ejangelico/SSRTeensy/widaq-magis-ssr-v2b/system_diagram.png

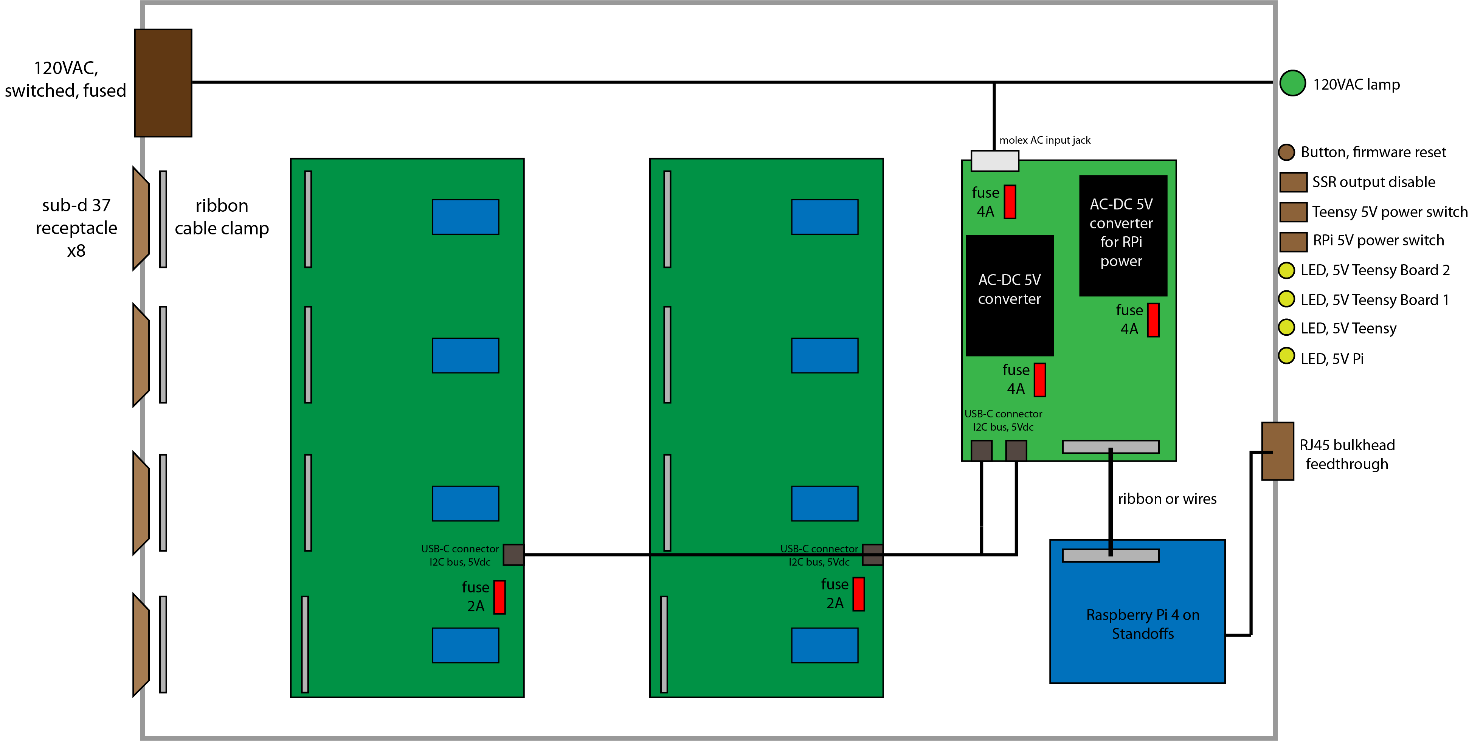
widaq-magis-ssr-v2b/system_diagram.png
