ejangelico/SSRTeensy/widaq-magis-ssr-v2b/assembly_diagrams/Screenshot 2023-06-01 at 9.44.38 AM.png

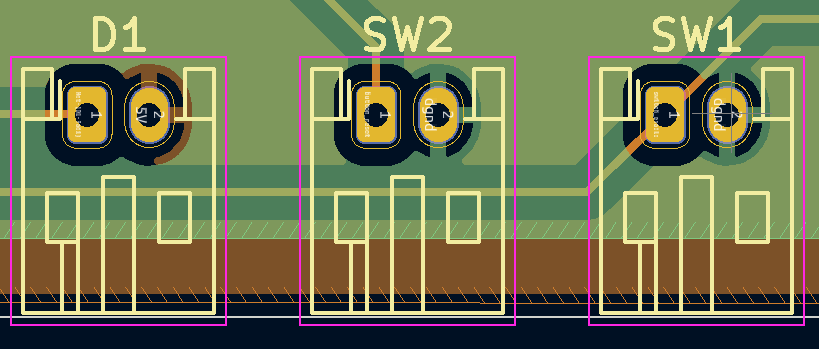
widaq-magis-ssr-v2b/assembly_diagrams/Screenshot 2023-06-01 at 9.44.38 AM.png
