ejangelico/SSRTeensy/widaq-magis-ssr-v2b/v2a-power-board/box-assembly/Screenshot 2023-04-19 at 4.38.34 PM.png

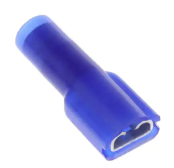
widaq-magis-ssr-v2b/v2a-power-board/box-assembly/Screenshot 2023-04-19 at 4.38.34 PM.png
