ejangelico/SSRTeensy/widaq-magis-ssr-v2b/output_files/2-21-22/widaq-magis-ssr-v1b-F_SilkS.pdf

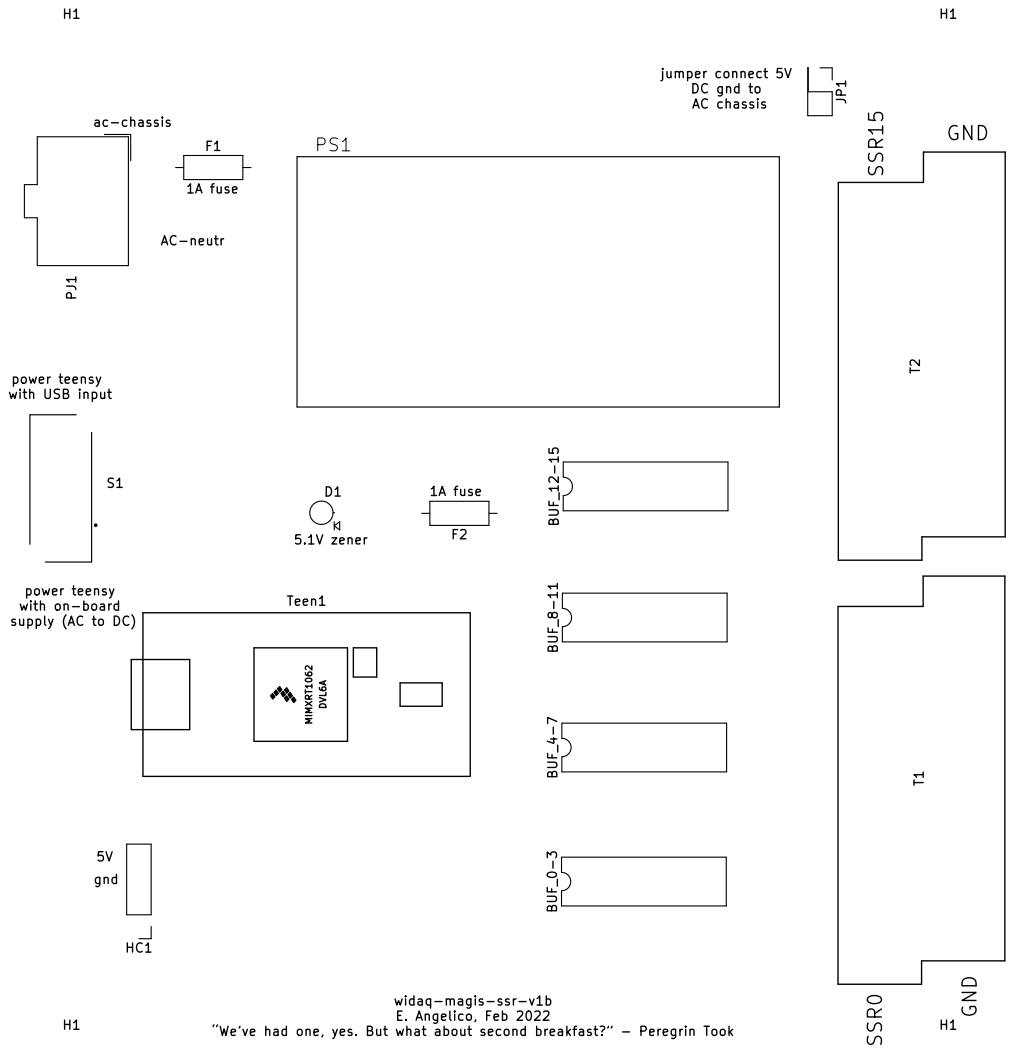
[picture p46: page 1]

jumper connect 5V DC gnd to AC chassis gnd

widaq-magis-ssr-v1b E. Angelico, Feb 2022 Weve had one, yes. But what about second breakfast? - Peregrin Took
