ejangelico/SSRTeensy/widaq-magis-ssr-v2b/output_files/drafting/widaq-magis-ssr-v1a.pdf

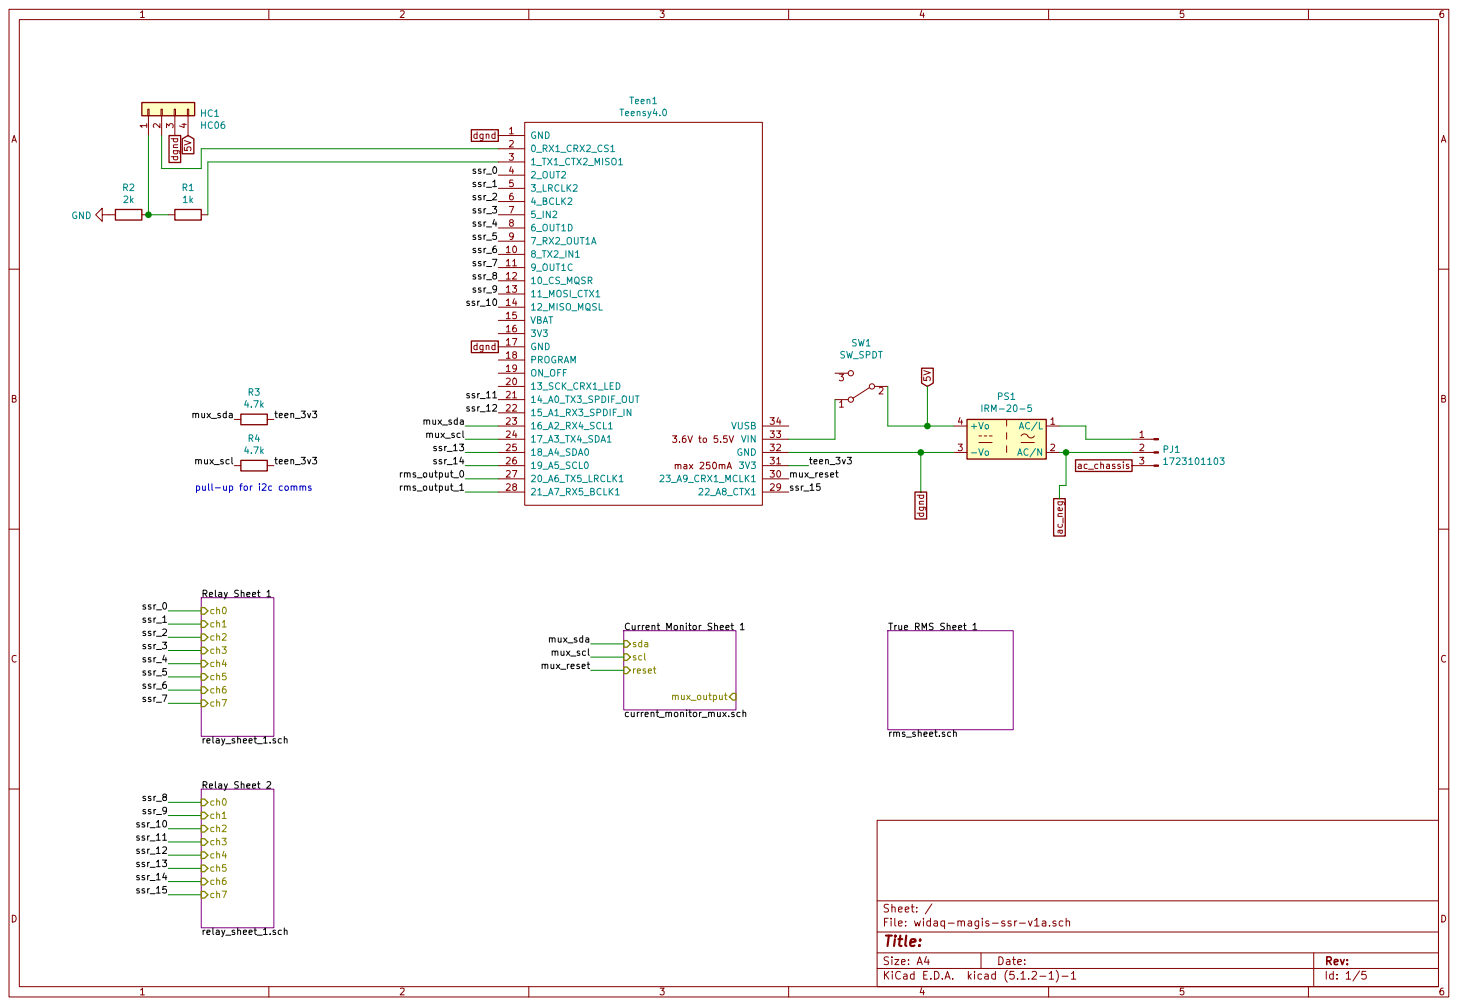
[picture p47: page 1]

pull-up for i2c comms

File: widaq-magis-ssr-v1a.sch Sheet: /

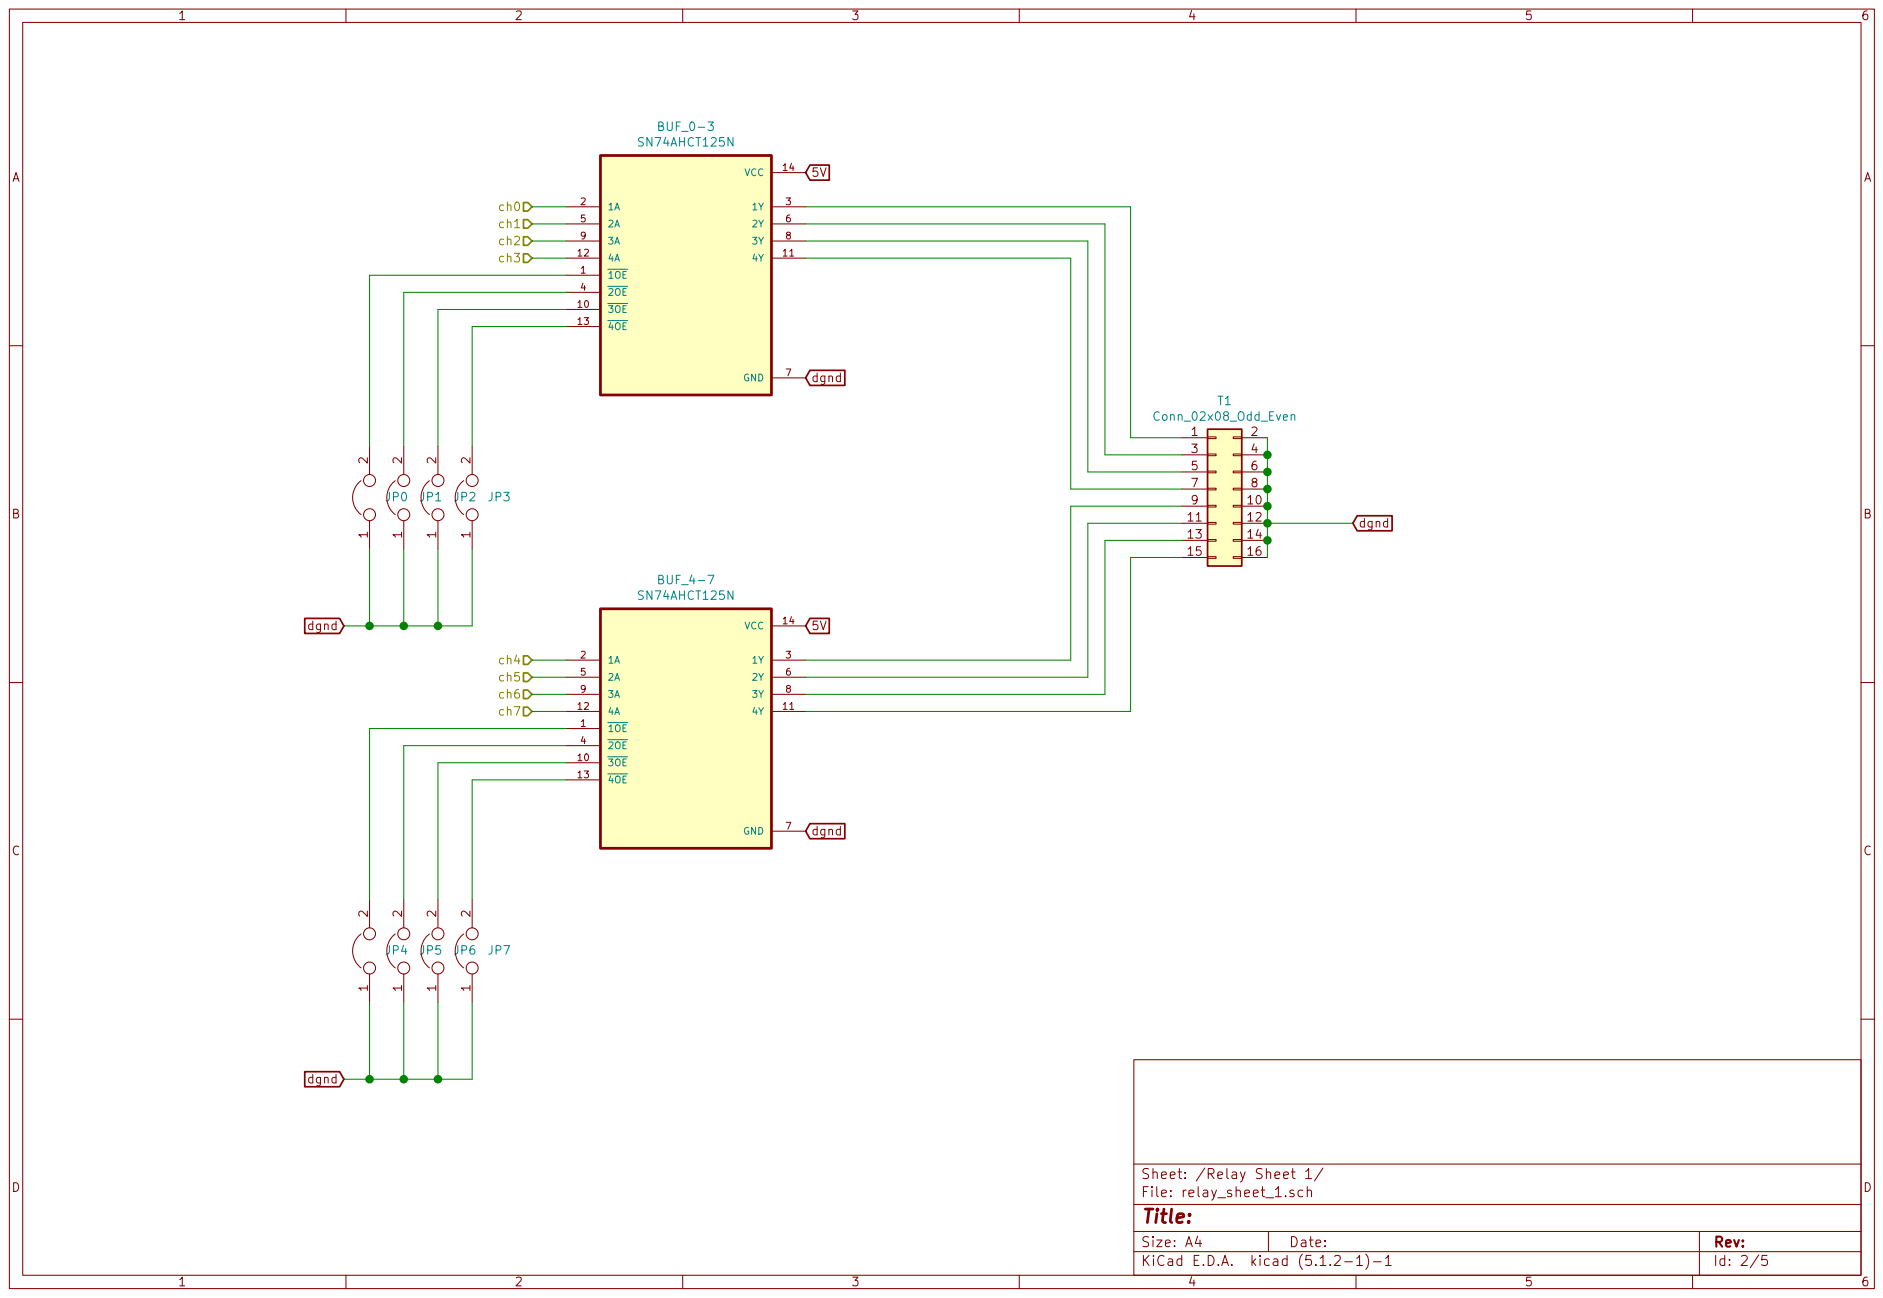
[picture p48: page 2]

11 | 12
13 | 14

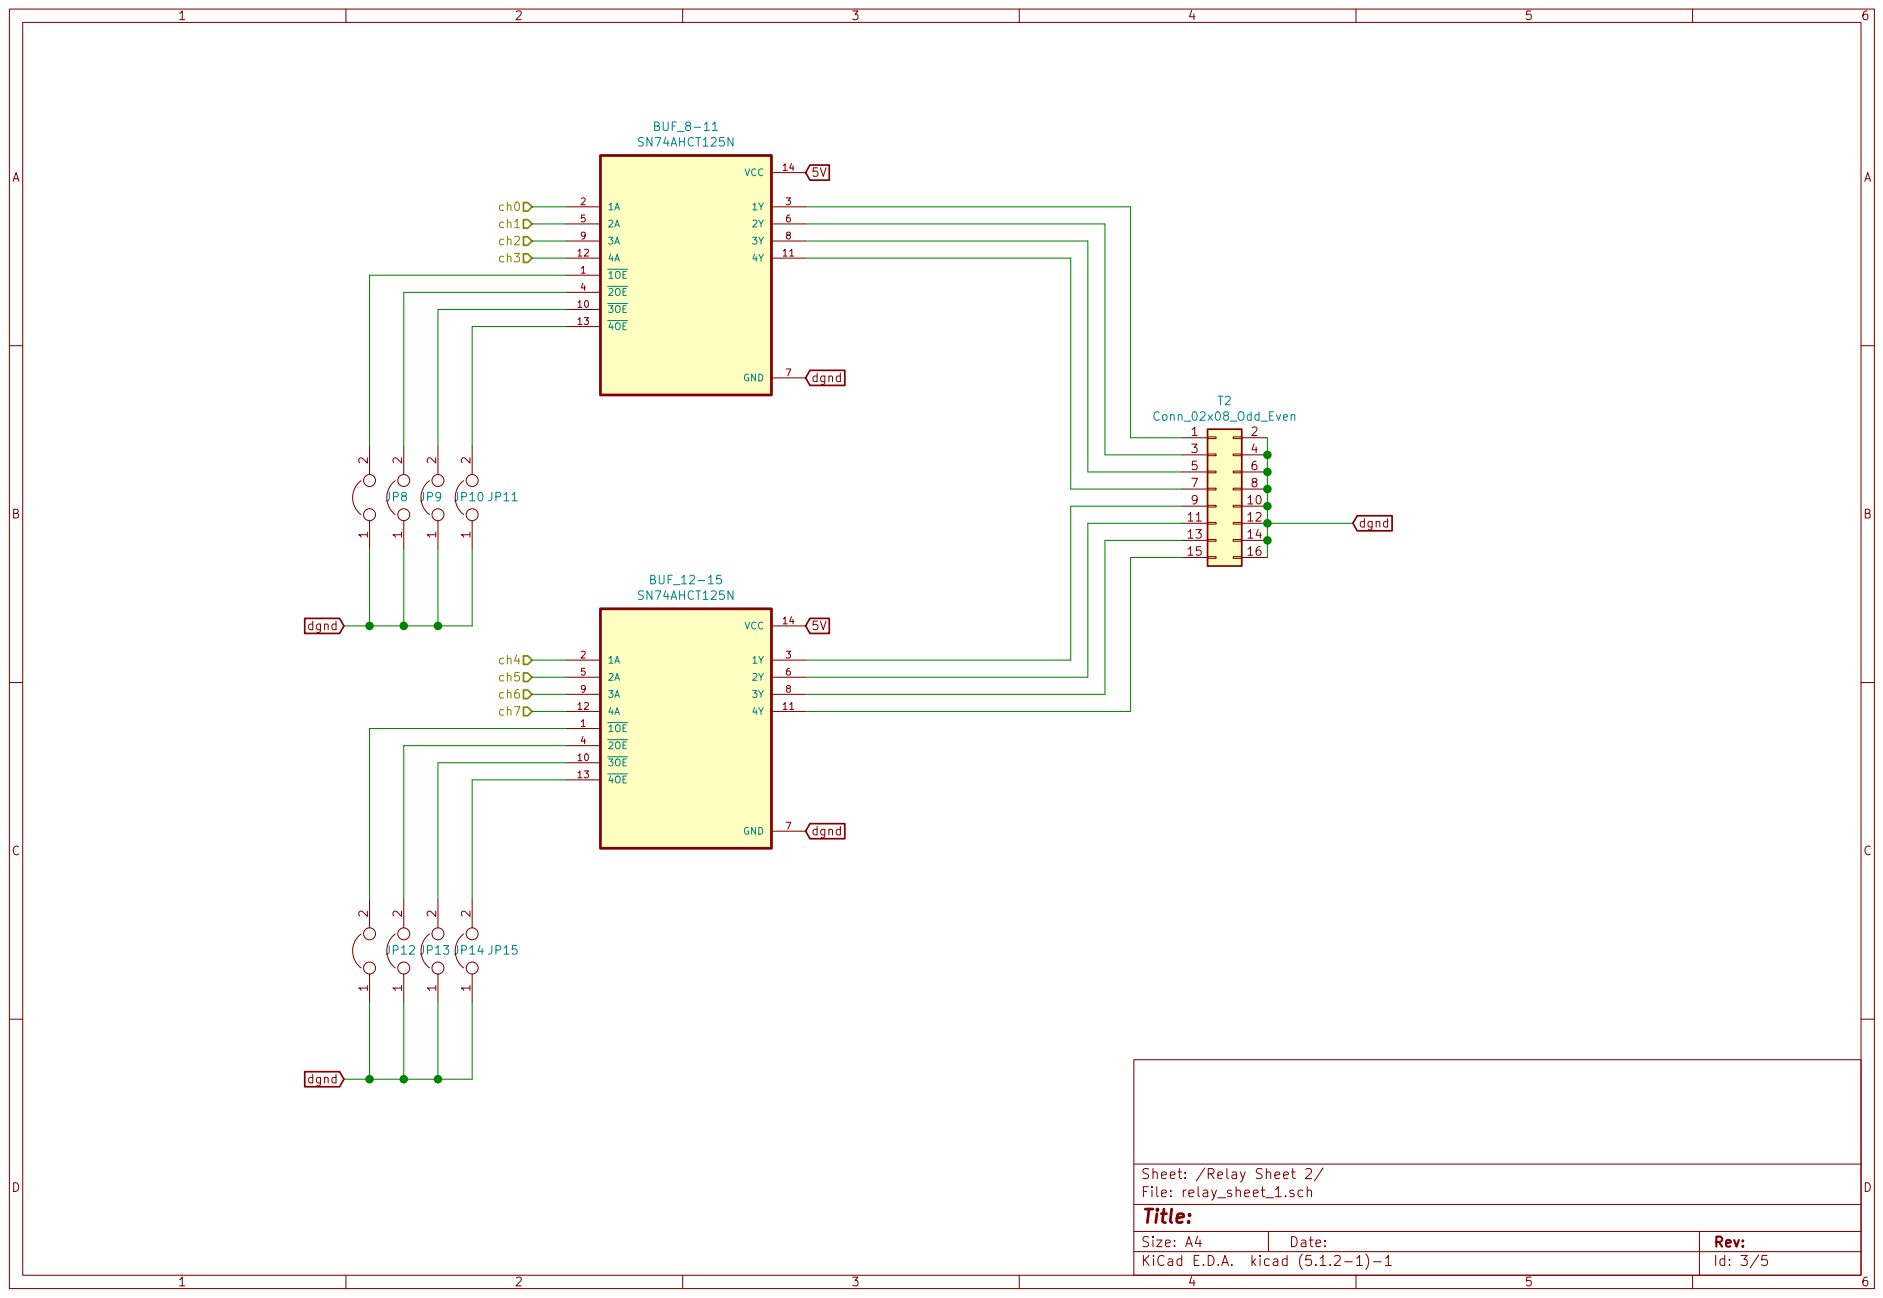
[picture p49: page 3]

11 | 12
13 | 14

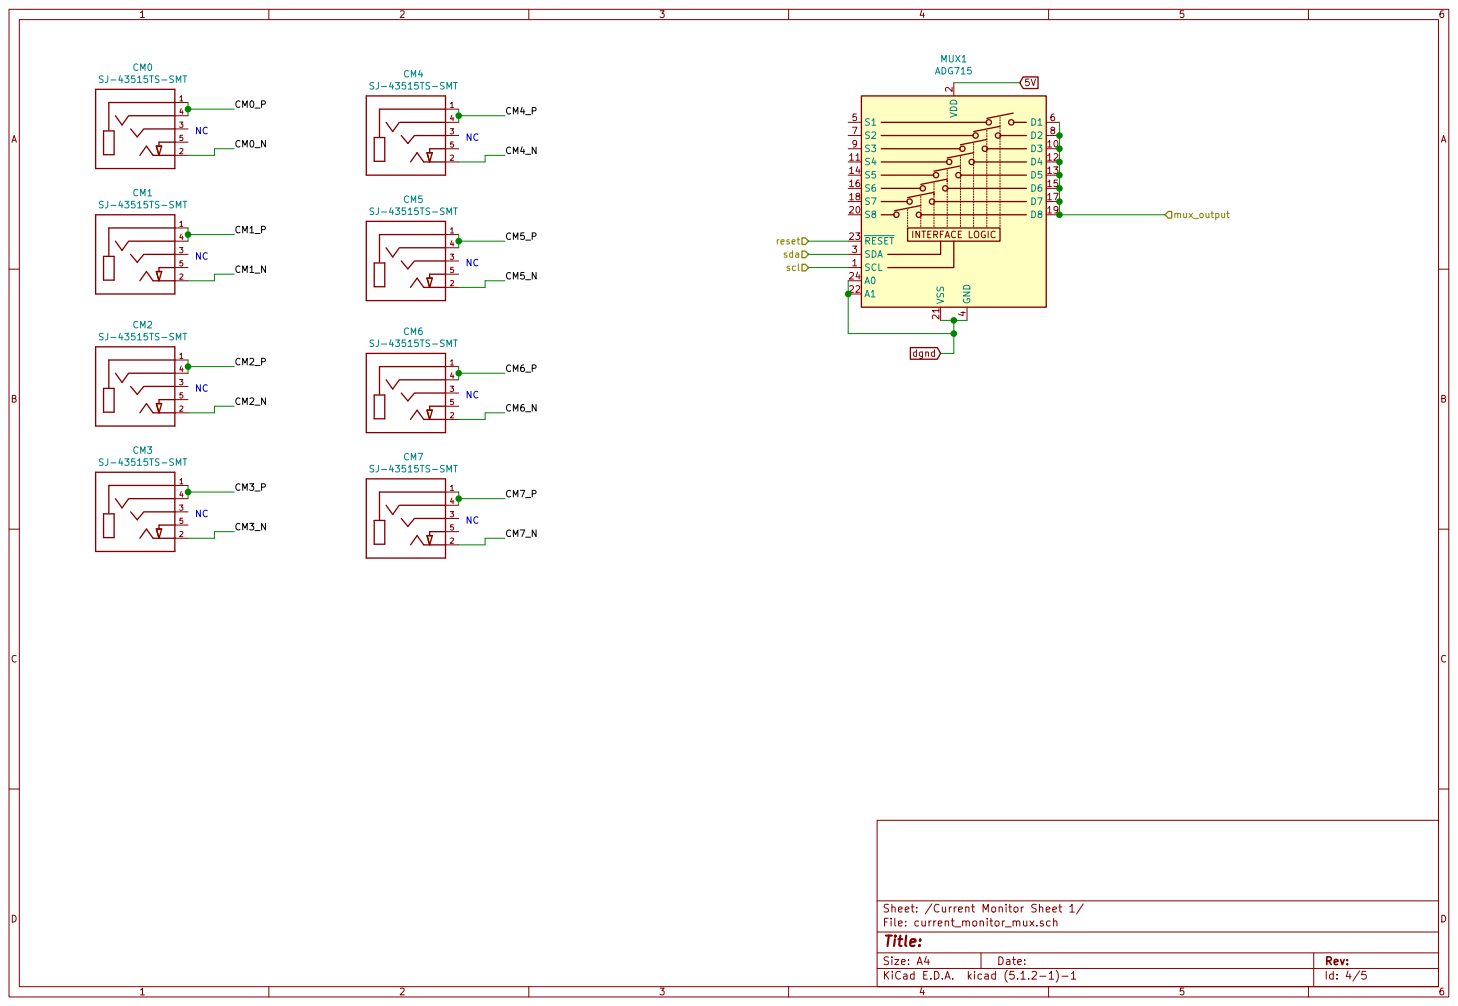
[picture p50: page 4]

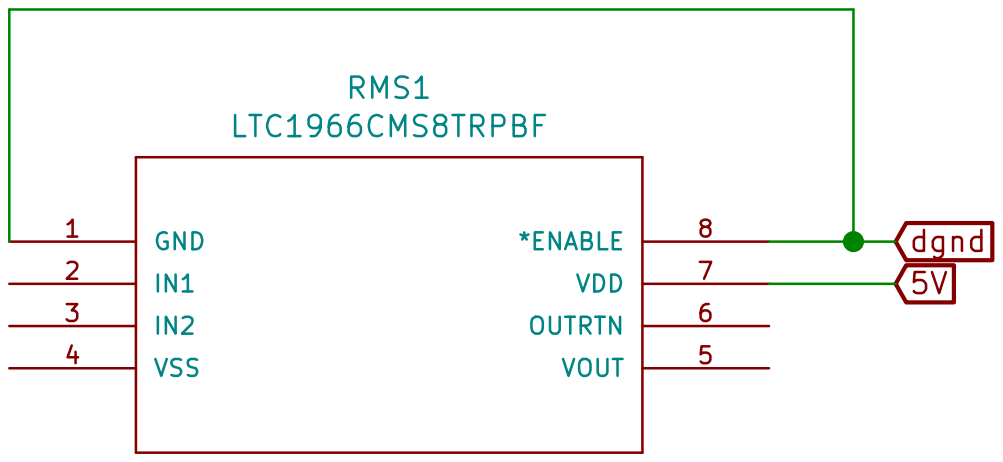
[picture p51: page 5]

File: rms_sheet.sch Sheet: /True RMS Sheet 1/
Id: 5/5 Title:
