ejangelico/SSRTeensy/widaq-magis-ssr-v2b/output_files/drafting/widaq-magis-ssr-v1b.pdf

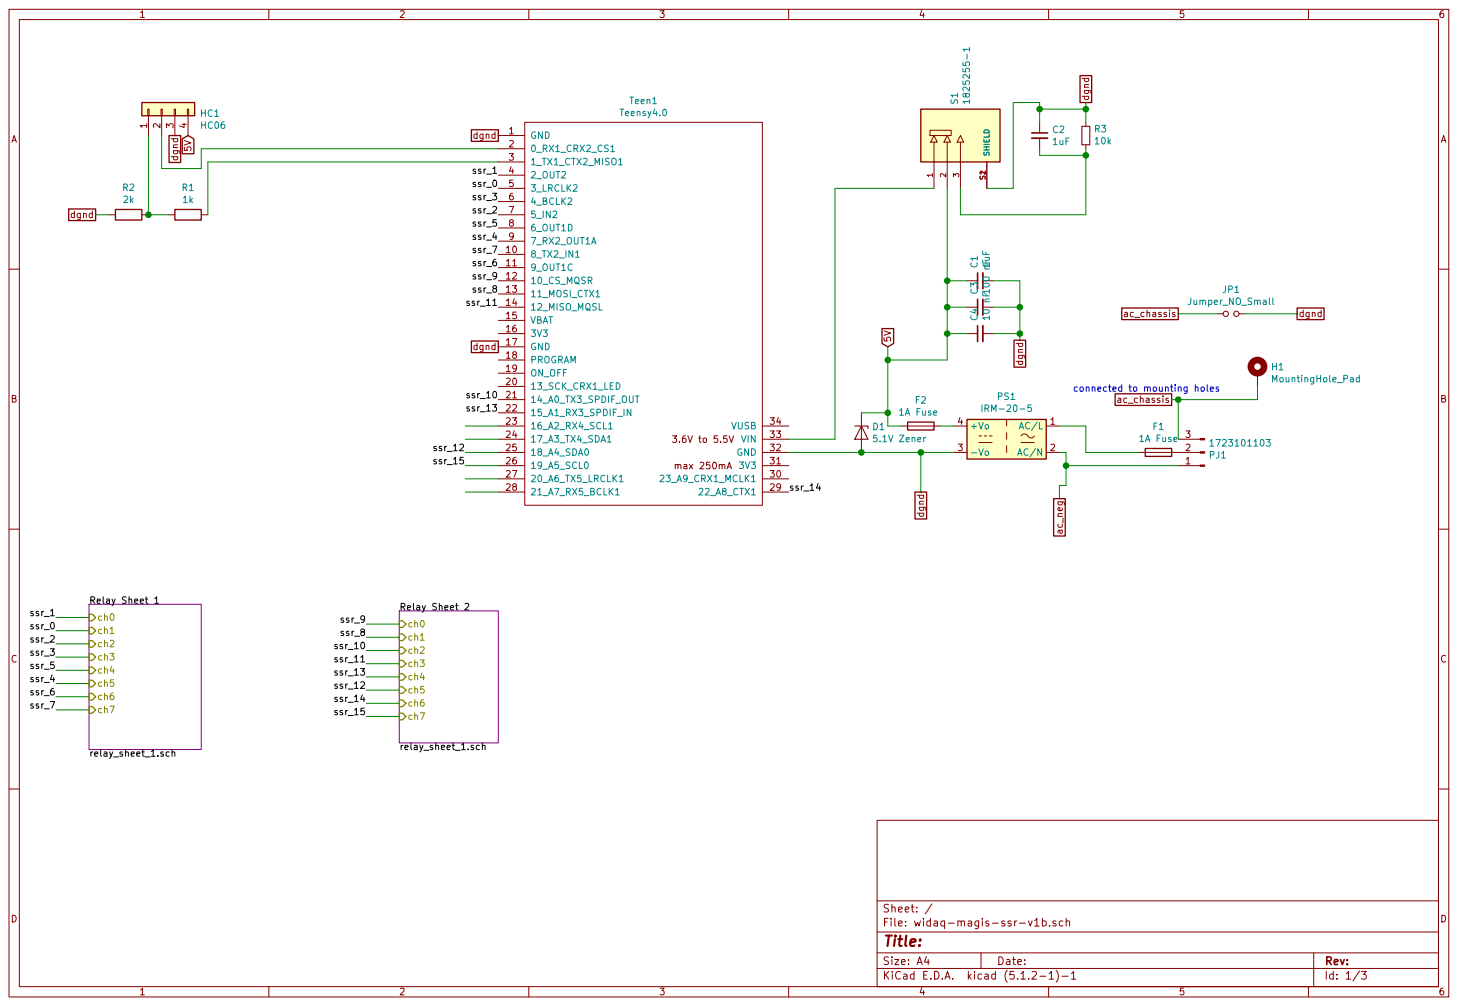
[picture p52: page 1]

connected to mounting holes

File: widaq-magis-ssr-v1b.sch Sheet: /
Id: 1/3 Title:
