ejangelico/SSRTeensy/widaq-magis-ssr-v2b/output_files/2-21-22/widaq-magis-ssr-v1b-F_Cu.pdf

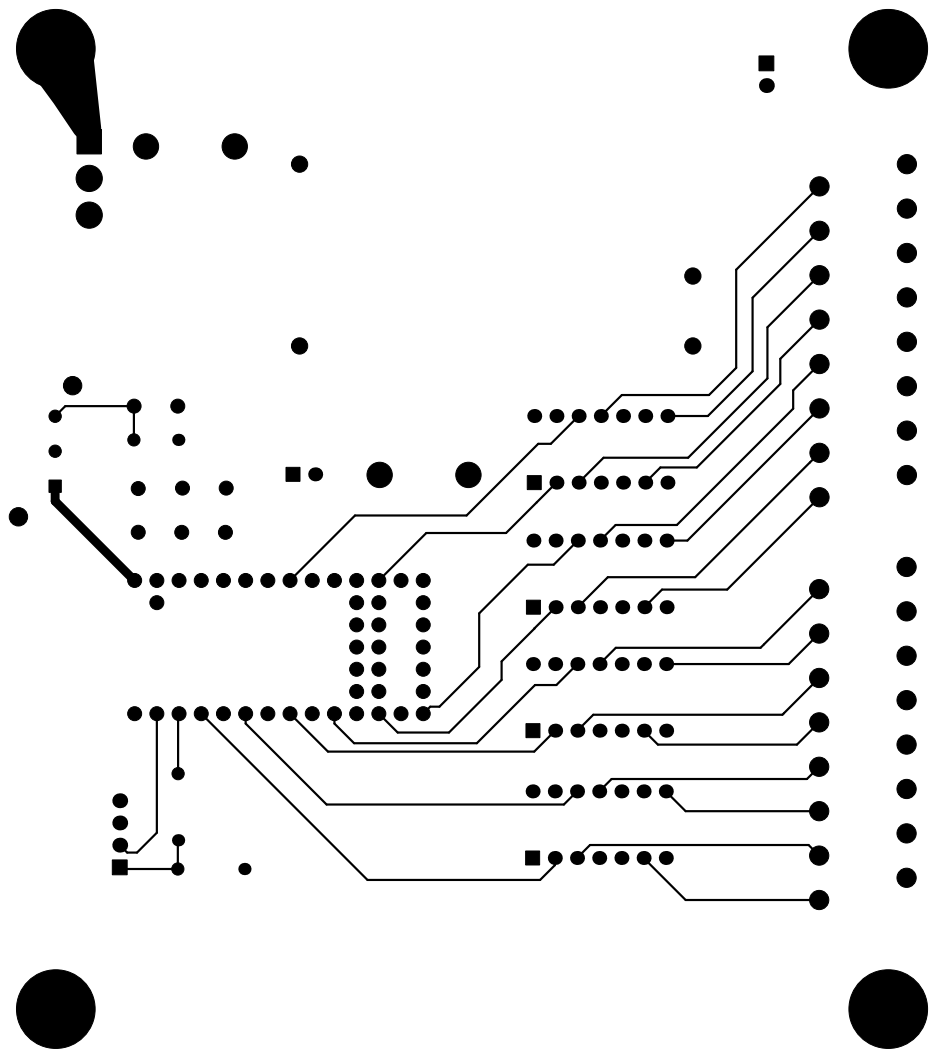
[picture p56: page 1]
