ejangelico/SSRTeensy/widaq-magis-ssr-v2b/output_files/2-21-22/widaq-magis-ssr-v1b-In1_Cu.pdf

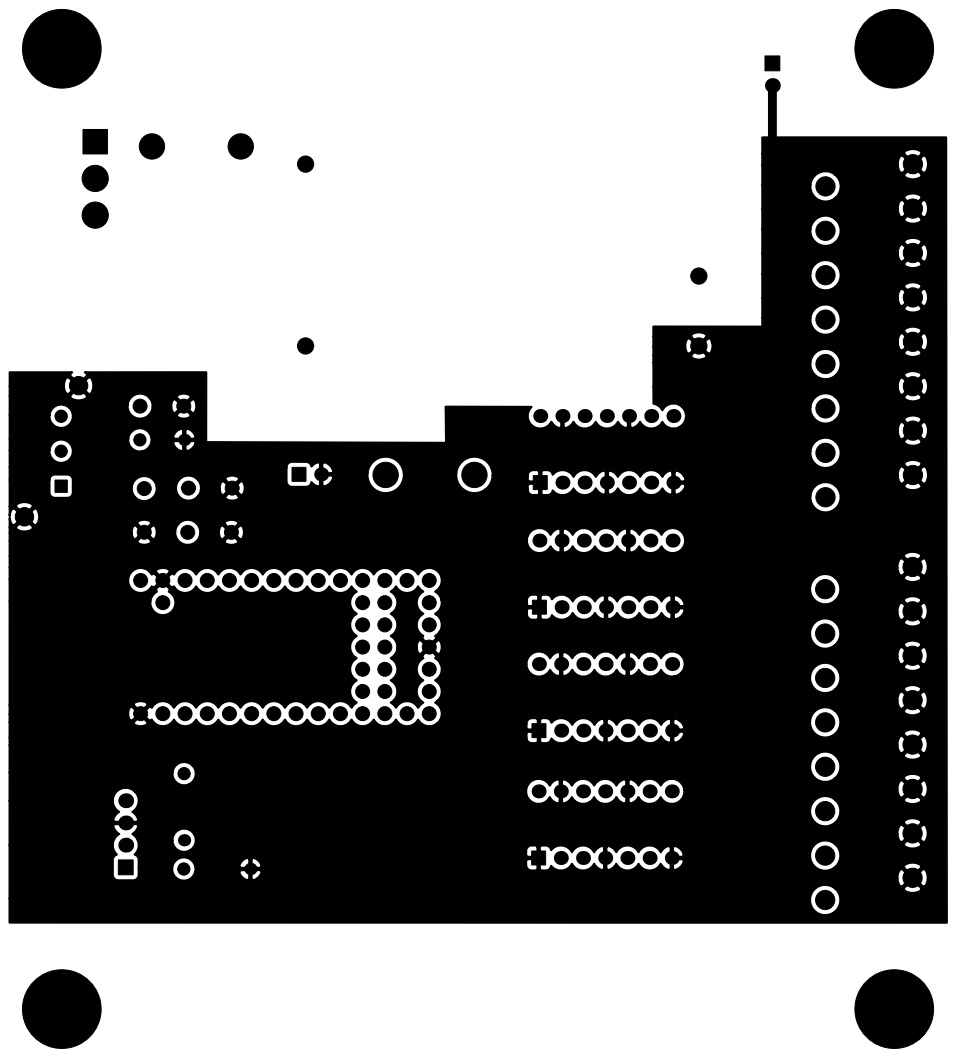
[picture p57: page 1]
