ejangelico/SSRTeensy/widaq-magis-ssr-v2b/output_files/2-21-22/widaq-magis-ssr-v1b-In2_Cu.pdf

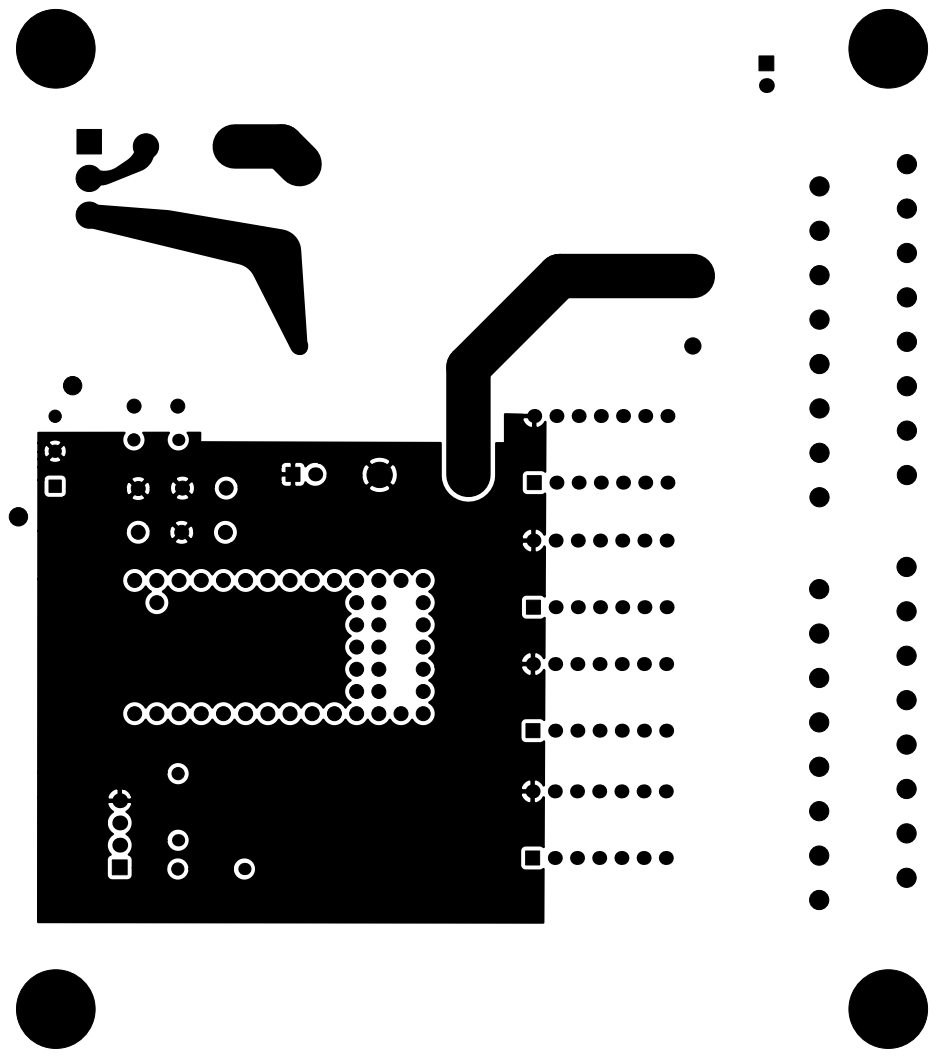
[picture p58: page 1]
