ejangelico/SSRTeensy/widaq-magis-ssr-v2b/output_files/7-22-22/widaq-magis-ssr-v2a-B_Cu.pdf

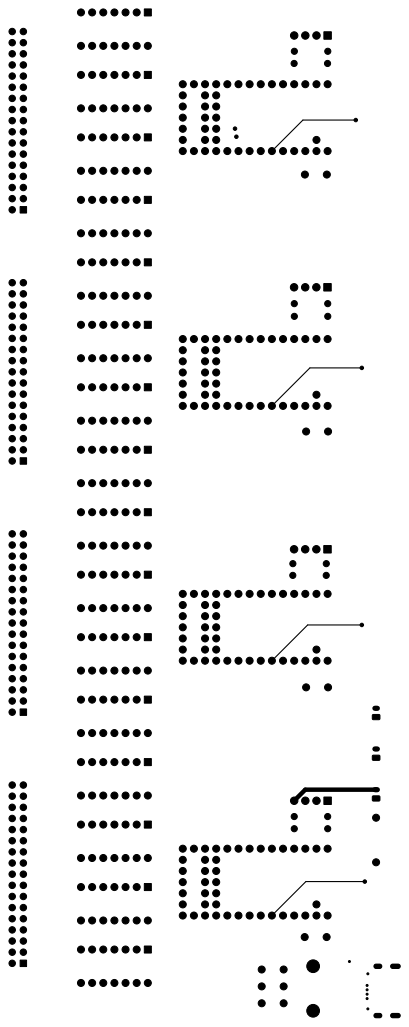
[picture p59: page 1]
