ejangelico/SSRTeensy/widaq-magis-ssr-v2b/output_files/7-22-22/widaq-magis-ssr-v2a-B_Mask.pdf

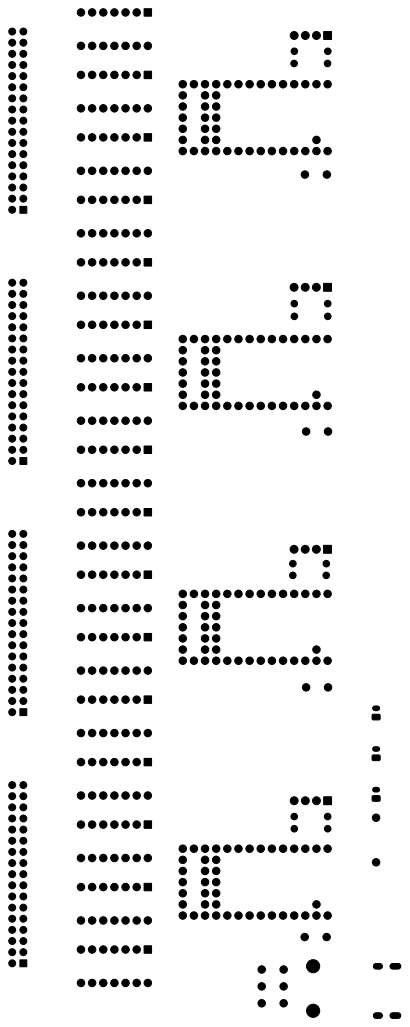
[picture p60: page 1]
