ejangelico/SSRTeensy/widaq-magis-ssr-v2b/output_files/7-22-22/widaq-magis-ssr-v2a-F_Mask.pdf

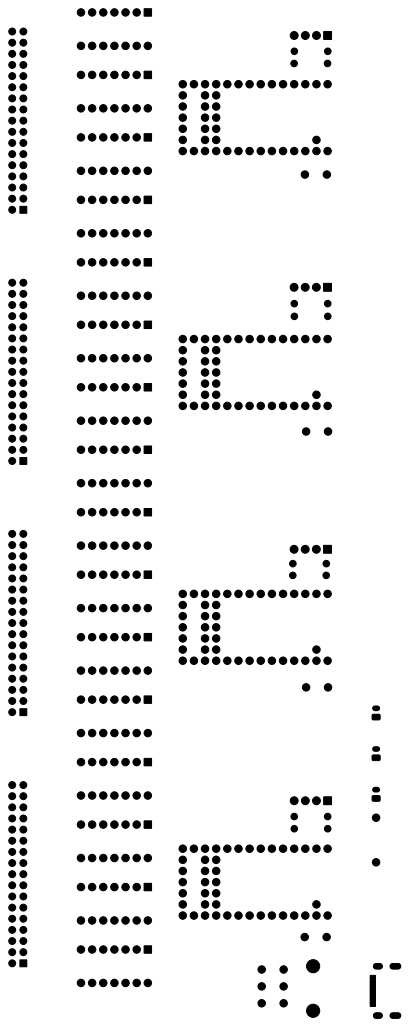
[picture p62: page 1]
