ejangelico/SSRTeensy/widaq-magis-ssr-v2b/output_files/7-22-22/widaq-magis-ssr-v2a-F_Silkscreen.pdf

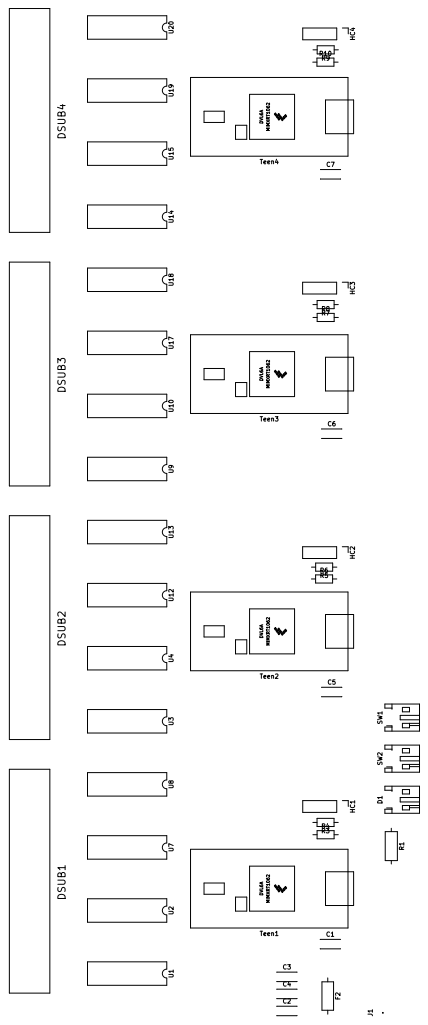
[picture p63: page 1]
