ejangelico/SSRTeensy/widaq-magis-ssr-v2b/output_files/2-13-23/pdfs/widaq-magis-ssr-v2b-B_Cu.pdf

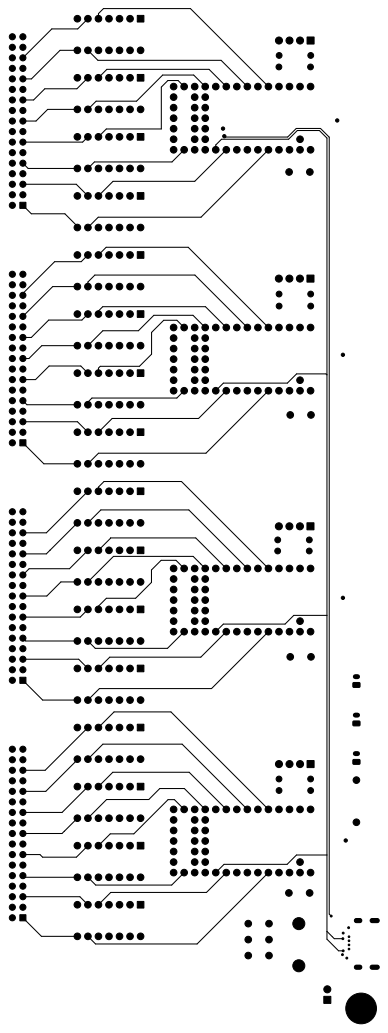
[picture p66: page 1]
