ejangelico/SSRTeensy/widaq-magis-ssr-v2b/output_files/2-13-23/pdfs/widaq-magis-ssr-v2b-B_Mask.pdf

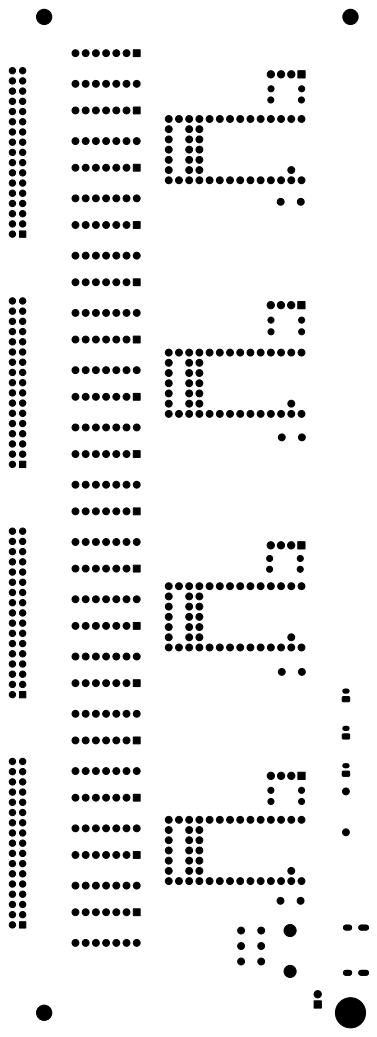
[picture p67: page 1]
