ejangelico/SSRTeensy/widaq-magis-ssr-v2b/output_files/2-13-23/pdfs/widaq-magis-ssr-v2b-Edge_Cuts.pdf

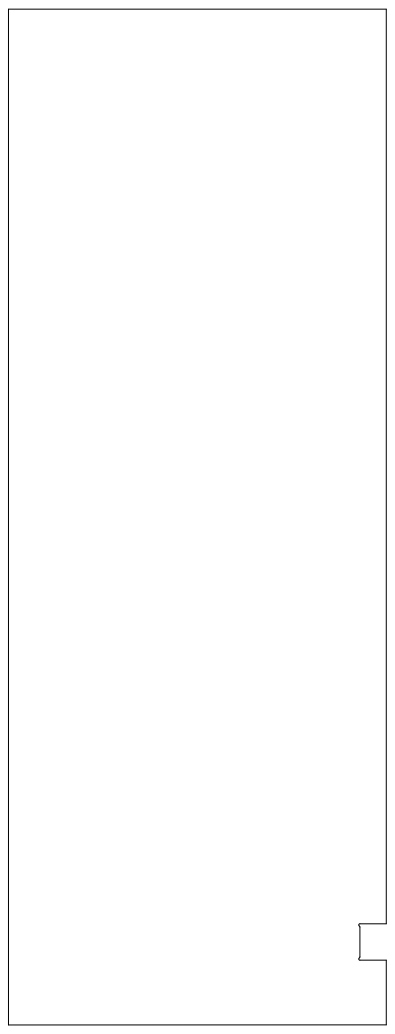
[picture p68: page 1]
