ejangelico/SSRTeensy/widaq-magis-ssr-v2b/output_files/2-13-23/pdfs/widaq-magis-ssr-v2b-F_Cu.pdf

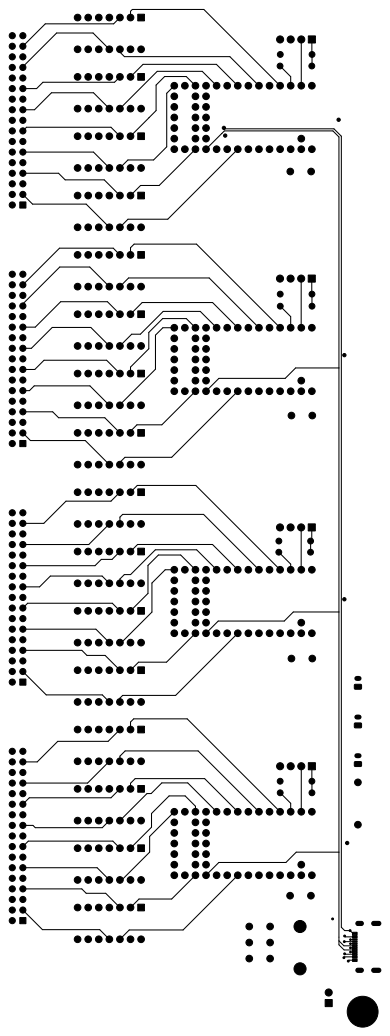
[picture p69: page 1]
