ejangelico/SSRTeensy/widaq-magis-ssr-v2b/output_files/2-13-23/pdfs/widaq-magis-ssr-v2b-F_Mask.pdf

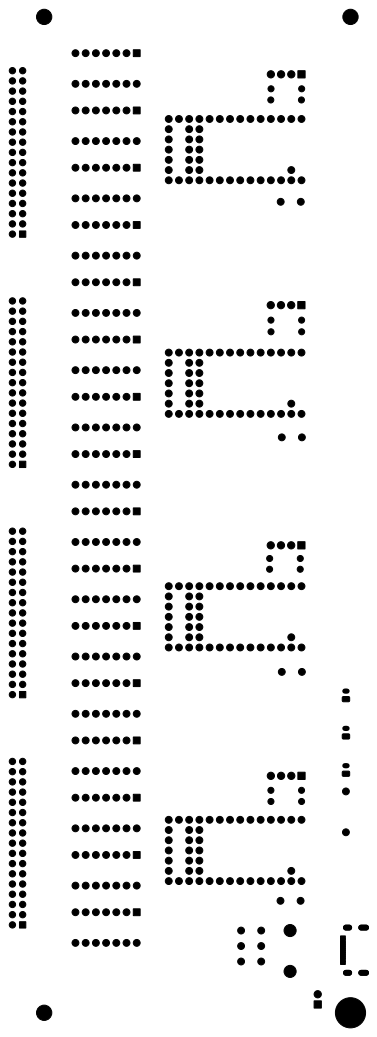
[picture p70: page 1]
