ejangelico/SSRTeensy/widaq-magis-ssr-v2b/output_files/2-13-23/pdfs/widaq-magis-ssr-v2b-F_Silkscreen.pdf

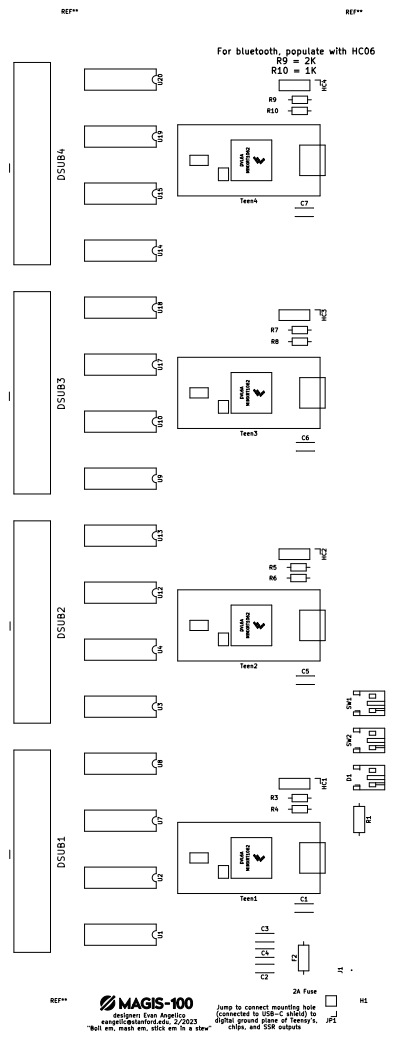
[picture p71: page 1]

For bluetooth, populate with HC06 R9 = 2K

(connected to USB-C shield) to
