ejangelico/SSRTeensy/widaq-magis-ssr-v2b/v2a-power-board/v2a-power-board-4/output_files/v2a-power-board-4-a/pdfs/v2a-power-board-4-F_Cu.pdf

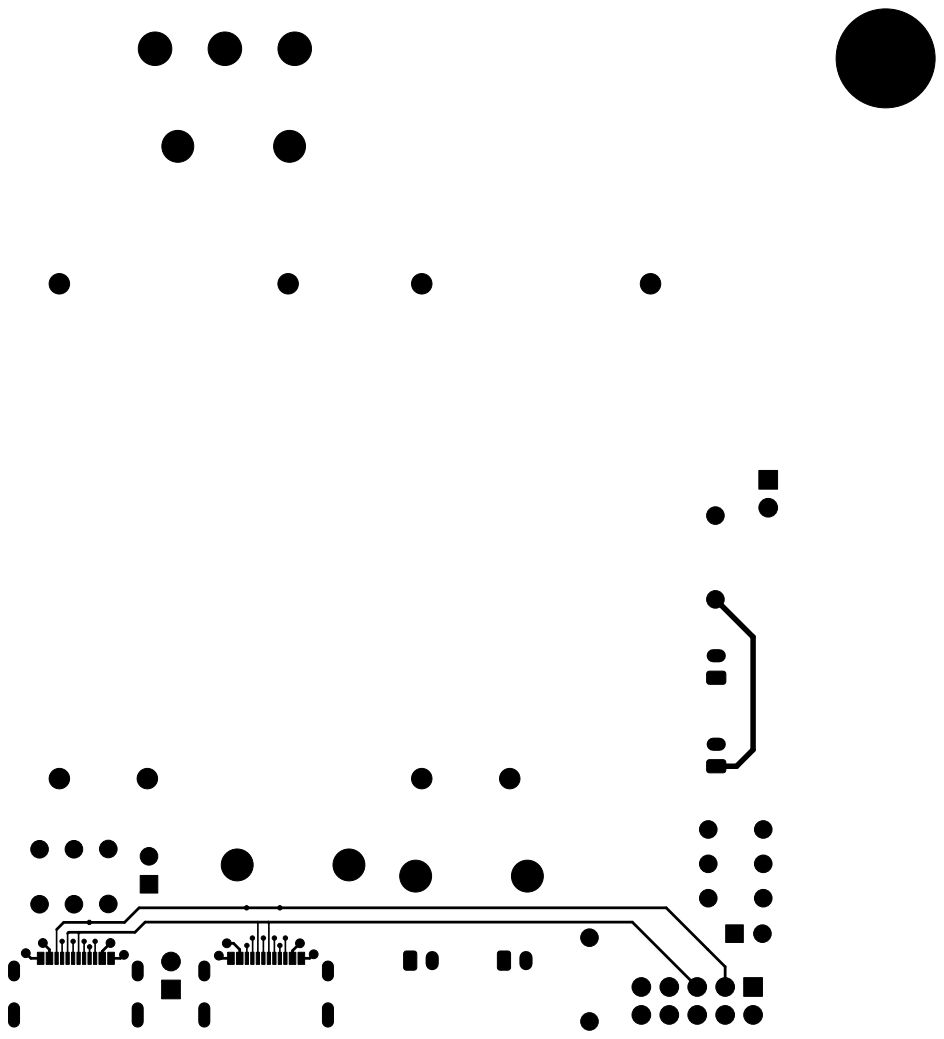
[picture p78: page 1]
