ejangelico/SSRTeensy/widaq-magis-ssr-v2b/ttl_opencollector_driver.asc

D1: LED; NSCW100
R1: res; 4.7e3
R2: res; 1e3
R3: res; 20
S1: sw; MYSW
U1: SN74LS07
V1: voltage; PULSE(0 3.3 0.001 0 0 0.03 0.2 3)
V2: voltage; 5
V3: voltage; 5
Named nets: 0
.tran 0.01 1
.model MYSW SW(Ron=1 Roff=1e9 Vt=3 Vh=-0.3)
